jrymk/gridfinity-eco/Rackfinity/STLs/trackMat_4.stl

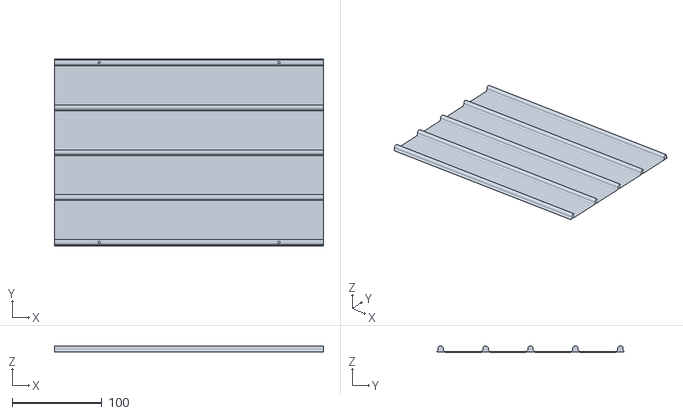
[picture p15: CAD file, 2024-02-13]
Rackfinity/STLs/trackMat_4.stl
299.5 x 208.4 x 7.20
