jrymk/gridfinity-eco/ClickPlates/ClickPlate-5x3.stl

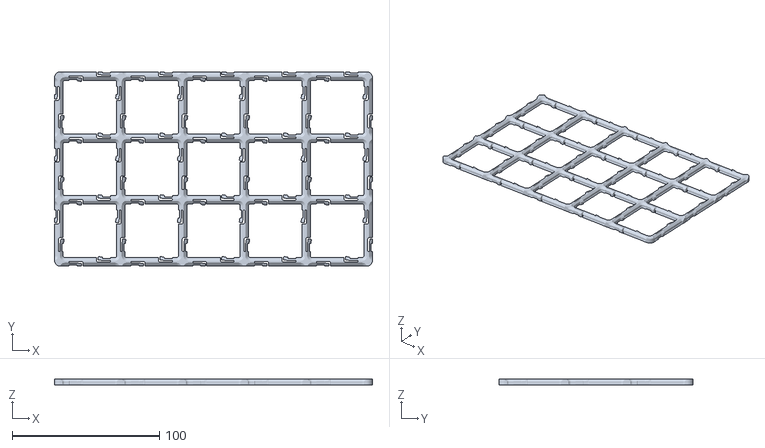
[picture p16: CAD file, 2023-03-19]
ClickPlates/ClickPlate-5x3.stl
216.0 x 132.0 x 4.00
