jrymk/gridfinity-eco/NormalPlates/frame5x4.stl

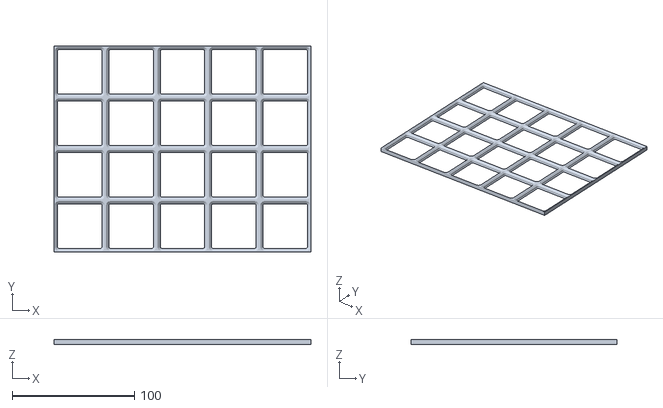
[picture p17: CAD file, 2023-08-11]
NormalPlates/frame5x4.stl
210.0 x 168.0 x 4.00
