jrymk/gridfinity-eco/ClickPlates/ClickPlate-5x2.stl

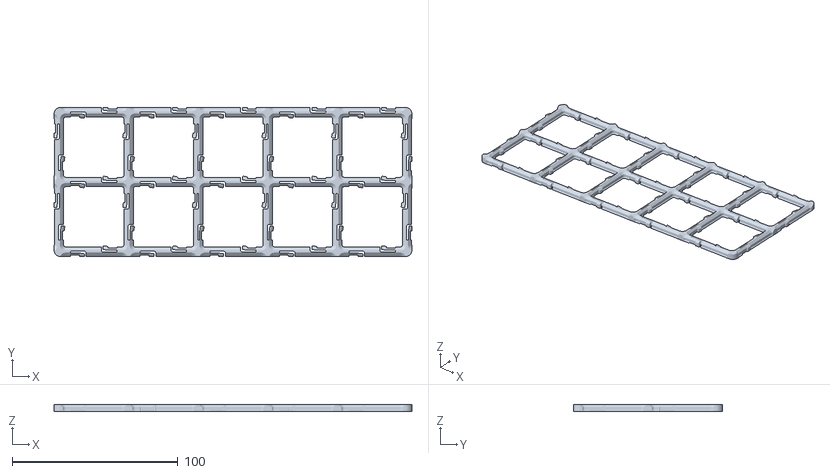
[picture p19: CAD file, 2023-03-19]
ClickPlates/ClickPlate-5x2.stl
216.0 x 90.0 x 4.00
