jrymk/gridfinity-eco/NormalPlates/frame5x3.stl

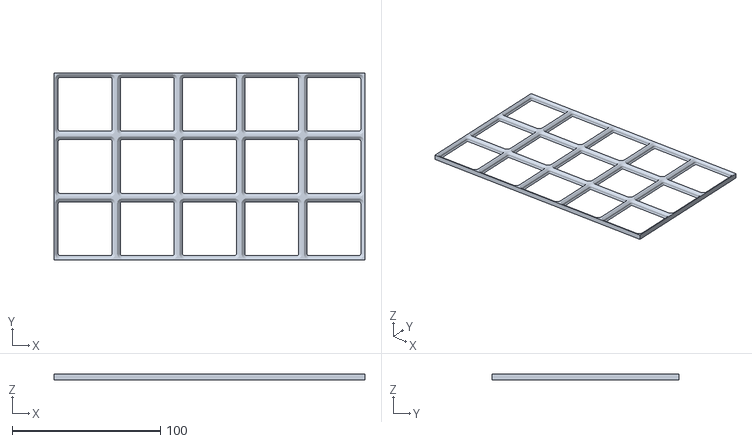
[picture p20: CAD file, 2023-08-11]
NormalPlates/frame5x3.stl
210.0 x 126.0 x 4.00
