jrymk/gridfinity-eco/PartsBinV2/1x2x6.stl

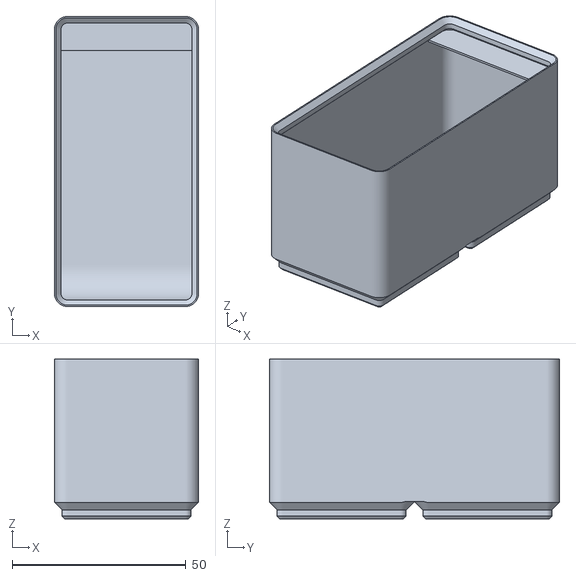
[picture p21: CAD file, 2023-06-26]
PartsBinV2/1x2x6.stl
41.5 x 83.5 x 46.0
