jrymk/gridfinity-eco/Rackfinity/STLs/14u-pla_only.stl

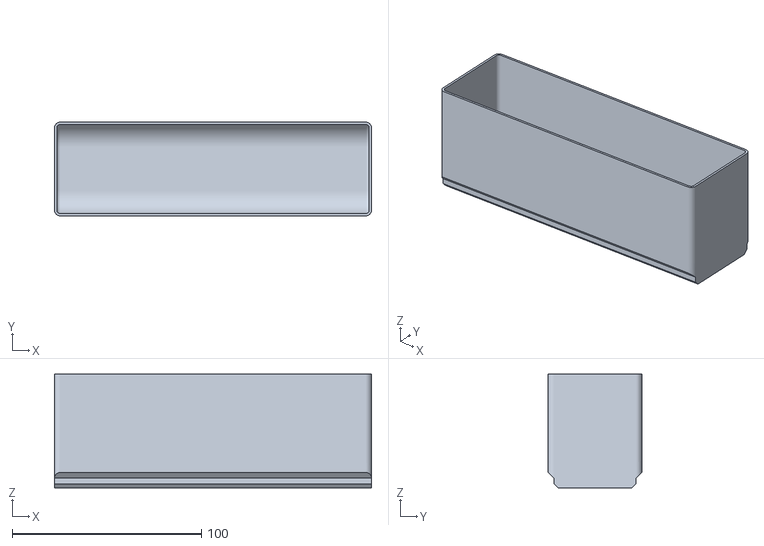
[picture p22: CAD file, 2024-02-13]
Rackfinity/STLs/14u-pla_only.stl
167.5 x 49.5 x 60.0
