jrymk/gridfinity-eco/ClickPlates/ClickPlate-5x4.stl

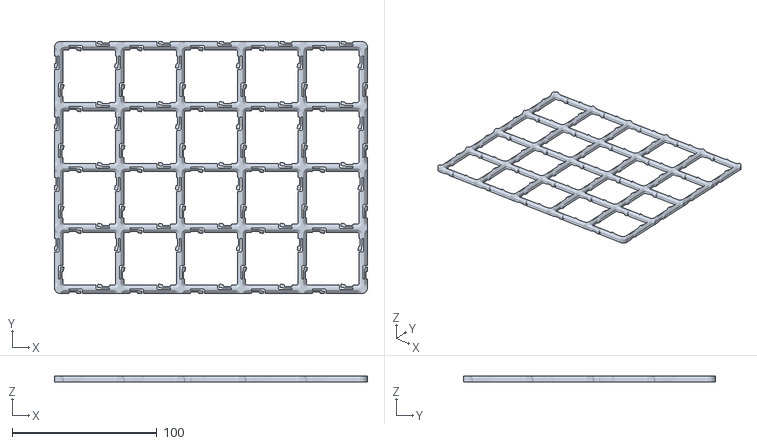
[picture p23: CAD file, 2023-03-19]
ClickPlates/ClickPlate-5x4.stl
216.0 x 174.0 x 4.00
