jrymk/gridfinity-eco/NormalPlates/frame3x3.stl

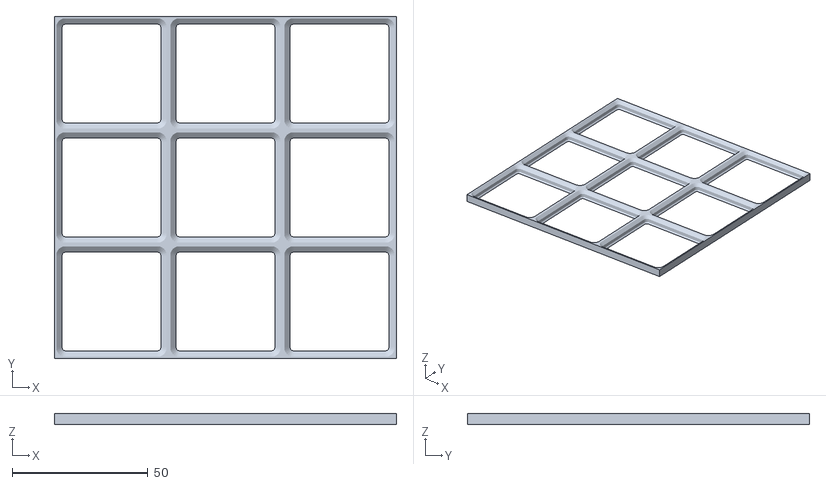
[picture p24: CAD file, 2023-08-11]
NormalPlates/frame3x3.stl
126.0 x 126.0 x 4.00
