jrymk/gridfinity-eco/PartsBinV2/2x1x3d3.stl

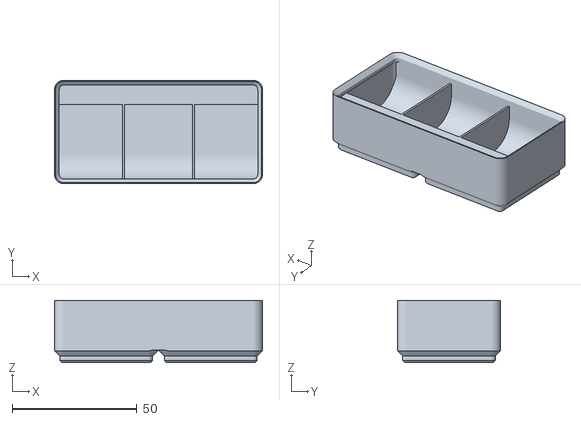
[picture p25: CAD file, 2023-06-26]
PartsBinV2/2x1x3d3.stl
83.5 x 41.5 x 25.0
