jrymk/gridfinity-eco/Rackfinity/STLs/18u-pla_only.stl

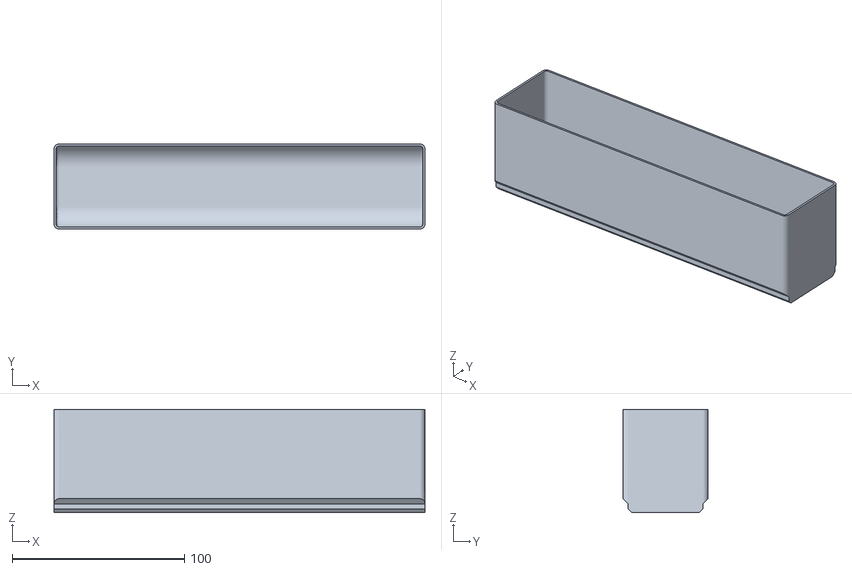
[picture p26: CAD file, 2024-02-13]
Rackfinity/STLs/18u-pla_only.stl
215.5 x 49.5 x 60.0
