jrymk/gridfinity-eco/PartsBinV2/1x3x6.stl

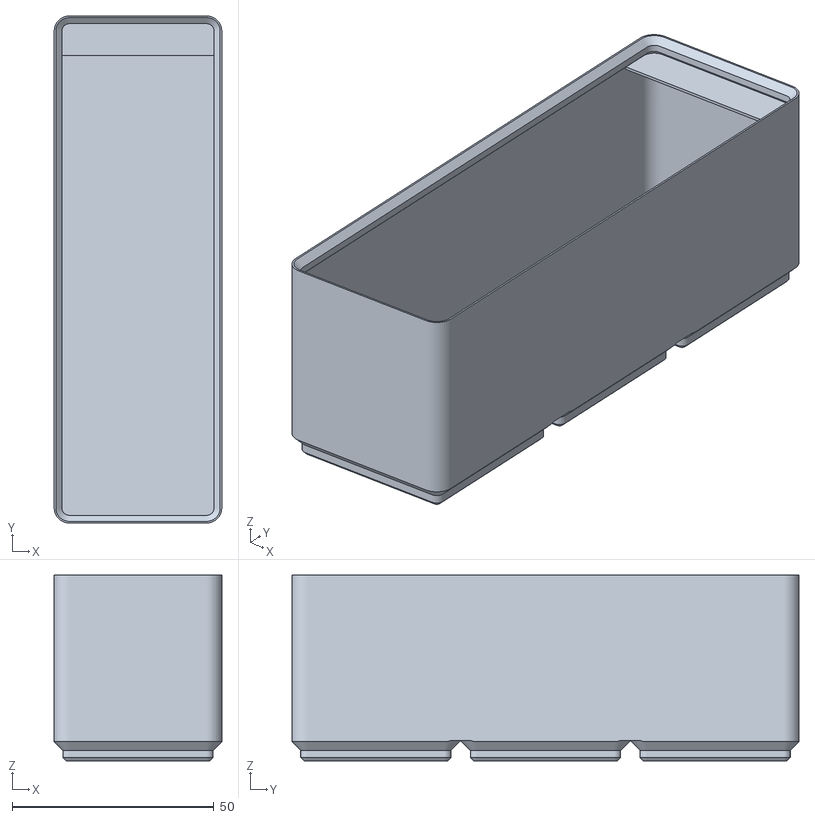
[picture p27: CAD file, 2023-06-26]
PartsBinV2/1x3x6.stl
41.5 x 125.5 x 46.0
