jrymk/gridfinity-eco/Rackfinity/STLs/drill guide.stl

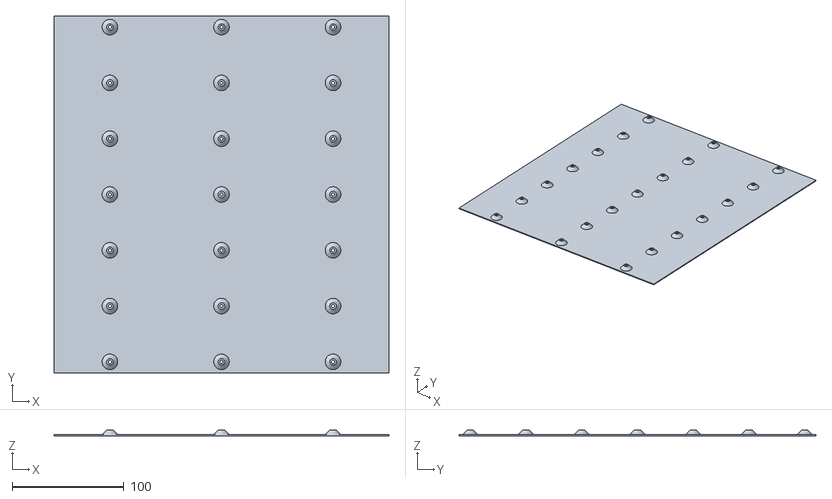
[picture p28: CAD file, 2024-02-13]
Rackfinity/STLs/drill guide.stl
300.0 x 320.0 x 5.00
