jrymk/gridfinity-eco/ClickPlates/ClickPlate-1x1.stl

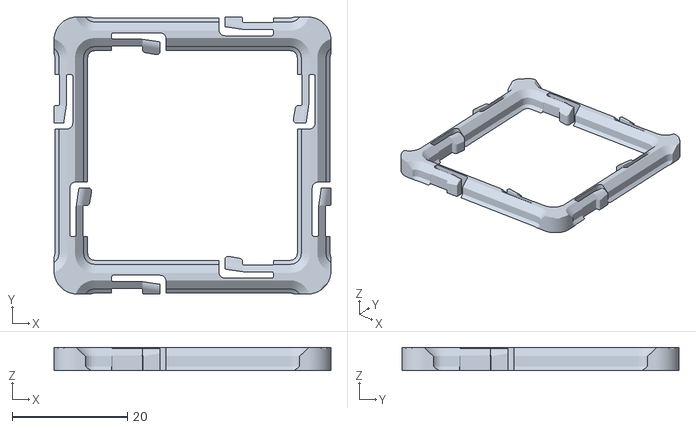
[picture p29: CAD file, 2023-03-19]
ClickPlates/ClickPlate-1x1.stl
48.0 x 48.0 x 4.00
