jrymk/gridfinity-eco/PartsBinV2/2x1x6.stl

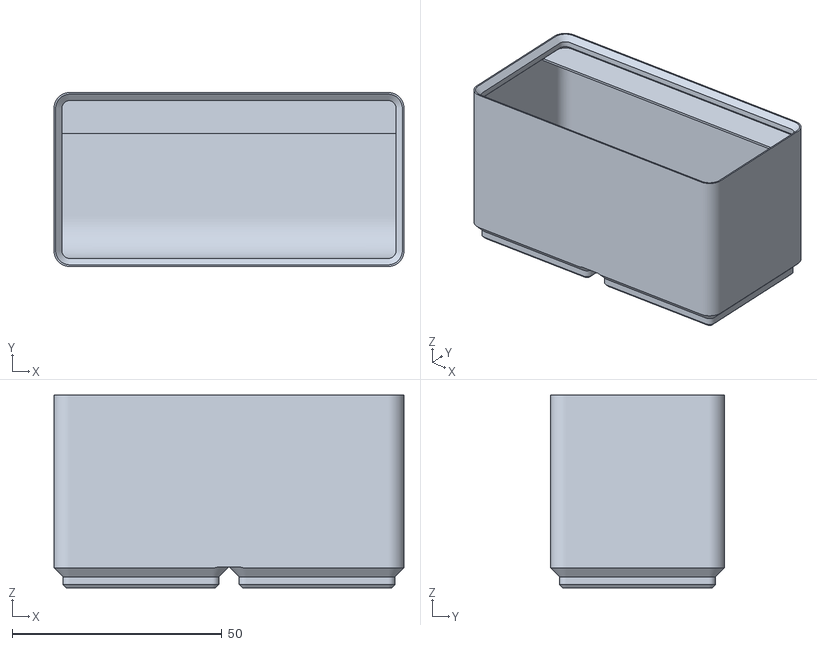
[picture p30: CAD file, 2023-06-26]
PartsBinV2/2x1x6.stl
83.5 x 41.5 x 46.0
