jrymk/gridfinity-eco/Rackfinity/STLs/16u-pla_only.stl

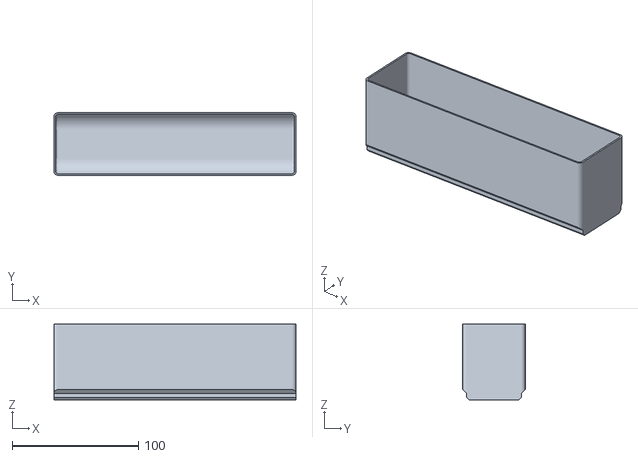
[picture p31: CAD file, 2024-02-13]
Rackfinity/STLs/16u-pla_only.stl
191.5 x 49.5 x 60.0
