jrymk/gridfinity-eco/ClickPlates/ClickPlate-3x2.stl

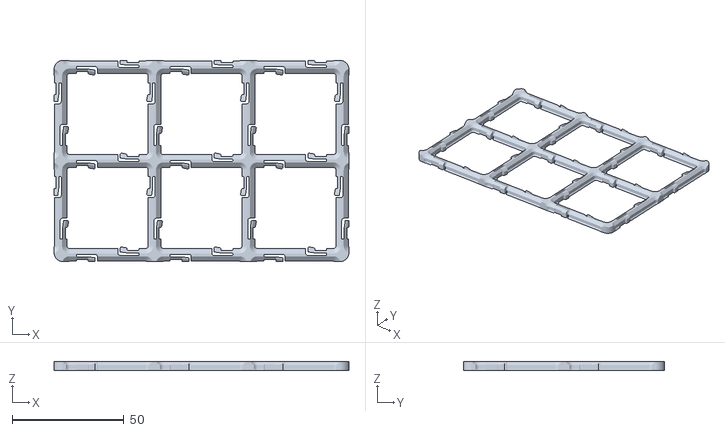
[picture p32: CAD file, 2023-03-19]
ClickPlates/ClickPlate-3x2.stl
132.0 x 90.0 x 4.00
