jrymk/gridfinity-eco/PartsBinV2/1x1x6.stl

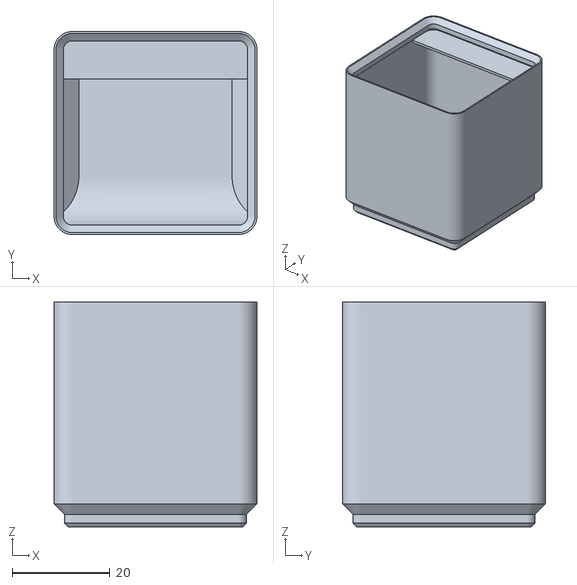
[picture p33: CAD file, 2023-06-26]
PartsBinV2/1x1x6.stl
41.5 x 41.5 x 46.0
