jrymk/gridfinity-eco/Rackfinity/STLs/12u-pla_only.stl

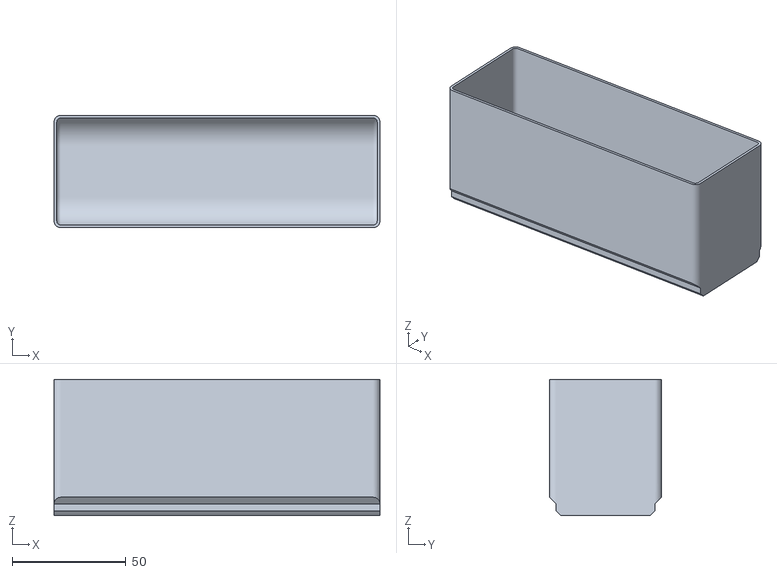
[picture p34: CAD file, 2024-02-13]
Rackfinity/STLs/12u-pla_only.stl
143.5 x 49.5 x 60.0
