jrymk/gridfinity-eco/ClickPlates/ClickPlate-4x4.stl

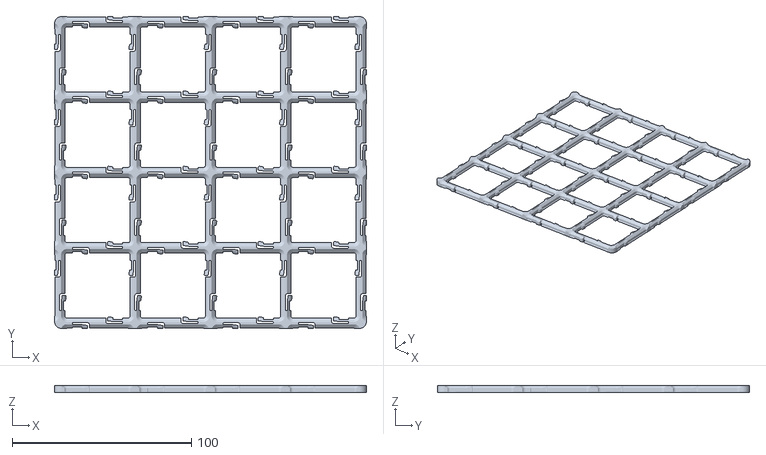
[picture p35: CAD file, 2023-03-19]
ClickPlates/ClickPlate-4x4.stl
174.0 x 174.0 x 4.00
