jrymk/gridfinity-eco/Rackfinity/STLs/trackMat_5.stl

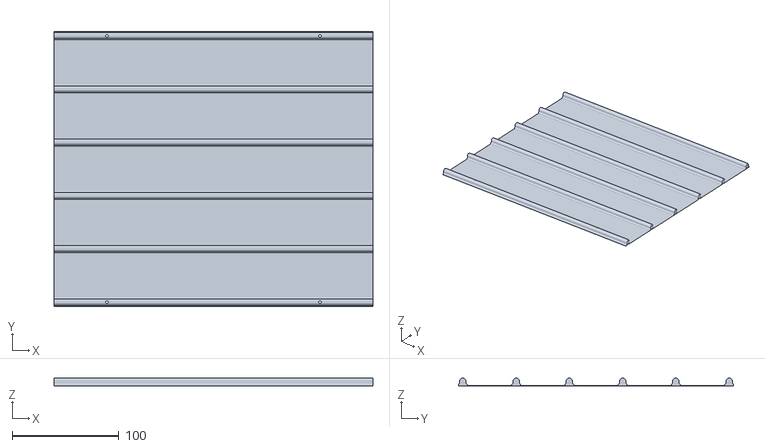
[picture p36: CAD file, 2024-02-13]
Rackfinity/STLs/trackMat_5.stl
299.5 x 258.4 x 7.20
