jrymk/gridfinity-eco/ClickPlates/ClickPlate-2x1.stl

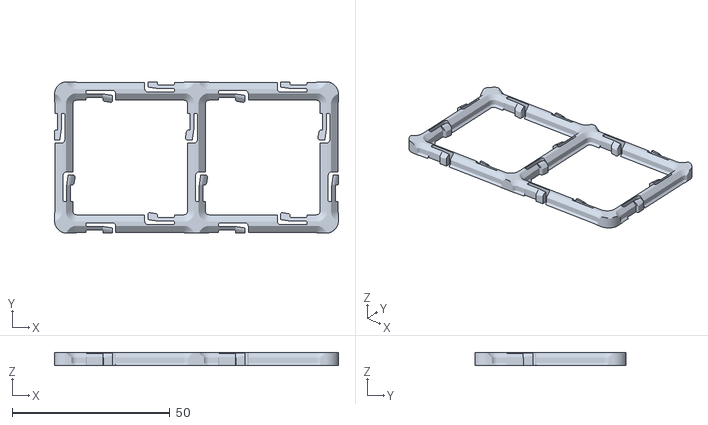
[picture p37: CAD file, 2023-03-19]
ClickPlates/ClickPlate-2x1.stl
90.0 x 48.0 x 4.00
