jrymk/gridfinity-eco/Rackfinity/STLs/8u.stl

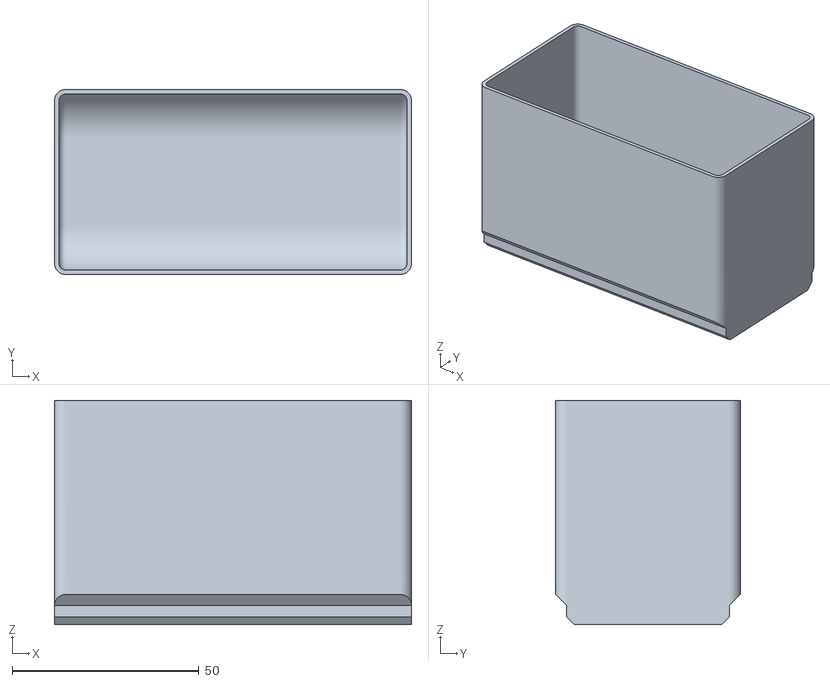
[picture p38: CAD file, 2024-02-13]
Rackfinity/STLs/8u.stl
95.5 x 49.5 x 60.0
