jrymk/gridfinity-eco/Rackfinity/STLs/20u-pla_only.stl

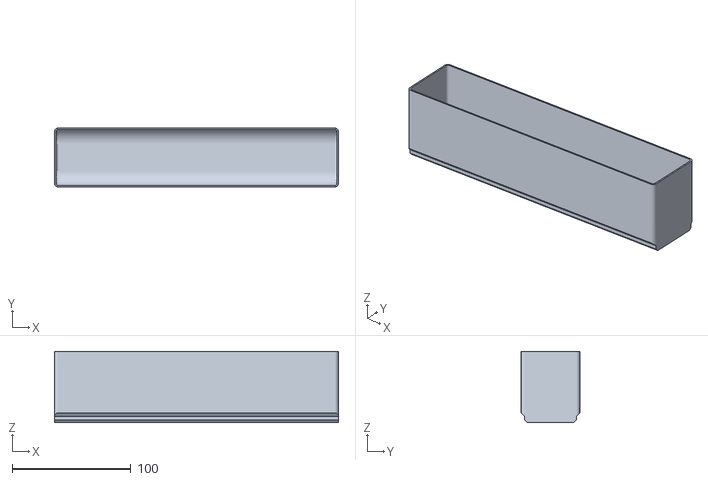
[picture p39: CAD file, 2024-02-13]
Rackfinity/STLs/20u-pla_only.stl
239.5 x 49.5 x 60.0
