jrymk/gridfinity-eco/ClickPlates/ClickPlate-3x1.stl

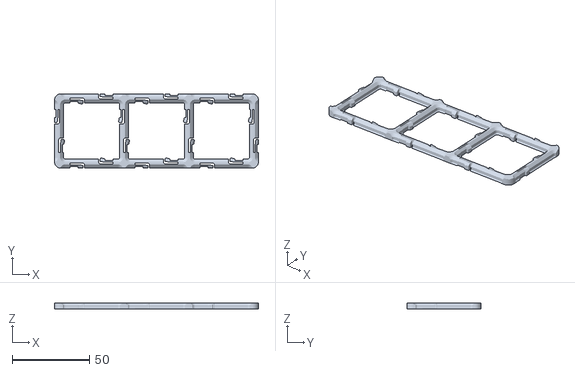
[picture p40: CAD file, 2023-03-19]
ClickPlates/ClickPlate-3x1.stl
132.0 x 48.0 x 4.00
