jrymk/gridfinity-eco/Rackfinity/STLs/3u.stl

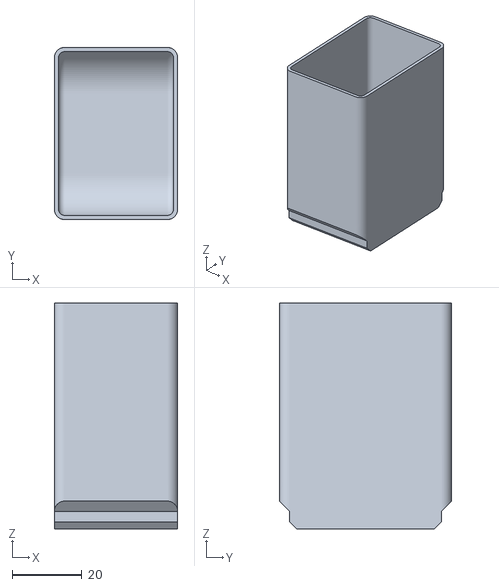
[picture p41: CAD file, 2024-01-20]
Rackfinity/STLs/3u.stl
35.5 x 49.5 x 65.0
