jrymk/gridfinity-eco/ClickPlates/ClickPlate-2x2.stl

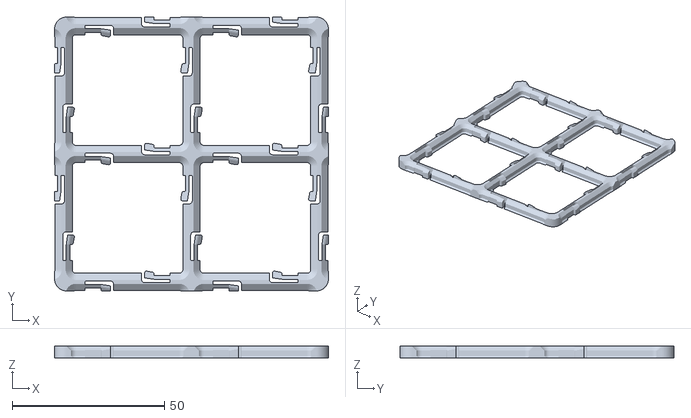
[picture p42: CAD file, 2023-03-19]
ClickPlates/ClickPlate-2x2.stl
90.0 x 90.0 x 4.00
