jrymk/gridfinity-eco/Rackfinity/STLs/side drill guide.stl

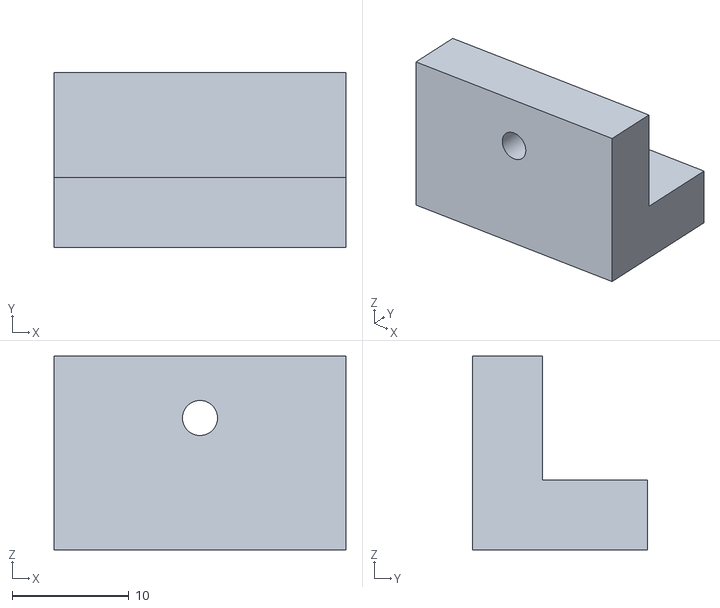
[picture p43: CAD file, 2024-01-20]
Rackfinity/STLs/side drill guide.stl
25.0 x 15.0 x 16.6
