jrymk/gridfinity-eco/ClickPlates/ClickPlate-4x3.stl

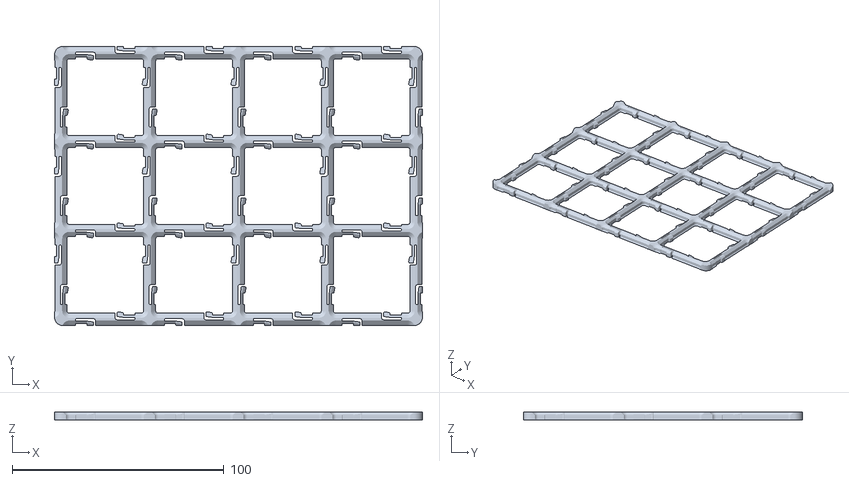
[picture p44: CAD file, 2023-03-19]
ClickPlates/ClickPlate-4x3.stl
174.0 x 132.0 x 4.00
