jrymk/gridfinity-eco/Rackfinity/STLs/2u.stl

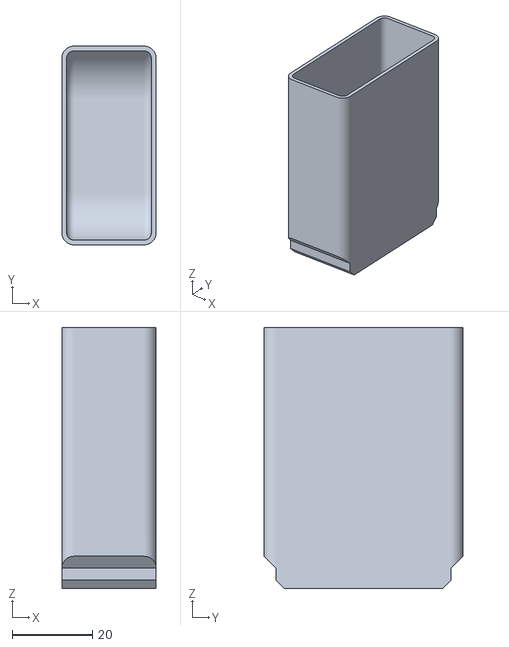
[picture p45: CAD file, 2024-01-20]
Rackfinity/STLs/2u.stl
23.5 x 49.5 x 65.0
