jrymk/gridfinity-eco/Rackfinity/STLs/4u.stl

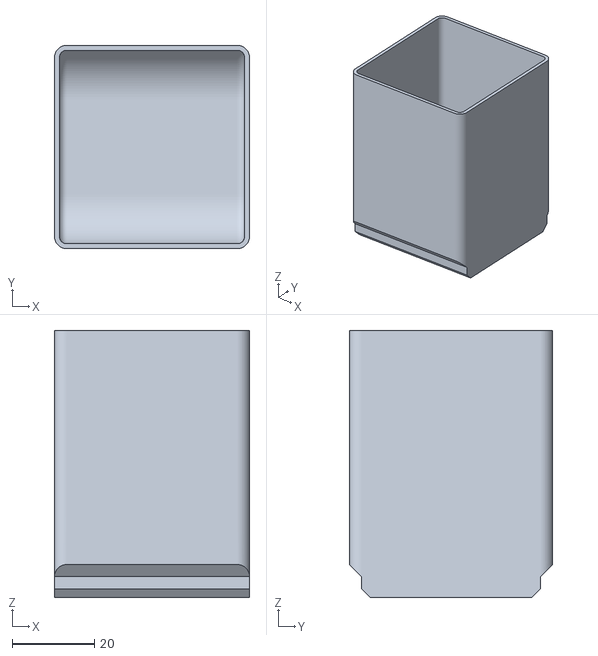
[picture p46: CAD file, 2024-01-20]
Rackfinity/STLs/4u.stl
47.5 x 49.5 x 65.0
